catid/voron/kinematic_bed_brush_riser/BrushRiser16mmBolts.stl

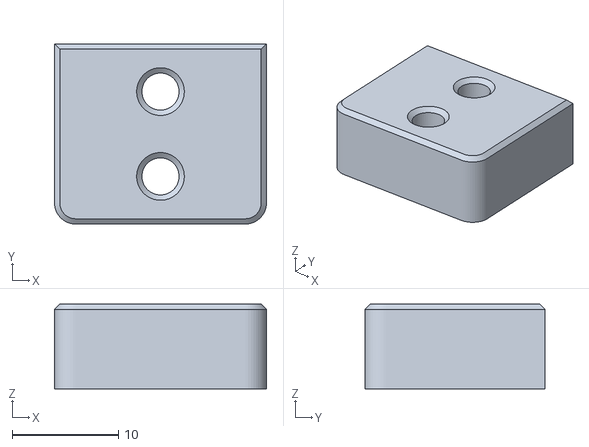
[picture p26: CAD file, 2022-04-16]
kinematic_bed_brush_riser/BrushRiser16mmBolts.stl
20.0 x 17.0 x 8.00
