catid/voron/printers/greenvoron/shaper_calibrate_x.png

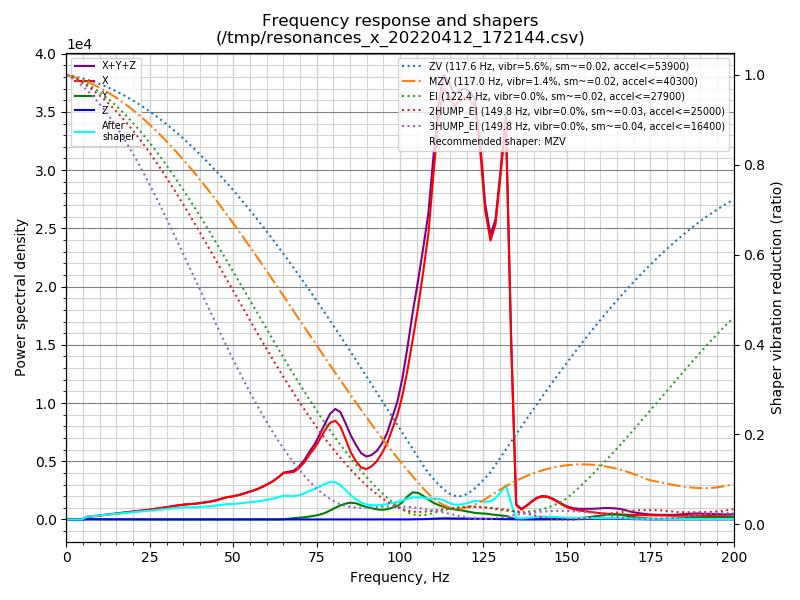
printers/greenvoron/shaper_calibrate_x.png
