catid/voron/printers/greenvoron/shaper_calibrate_y.png

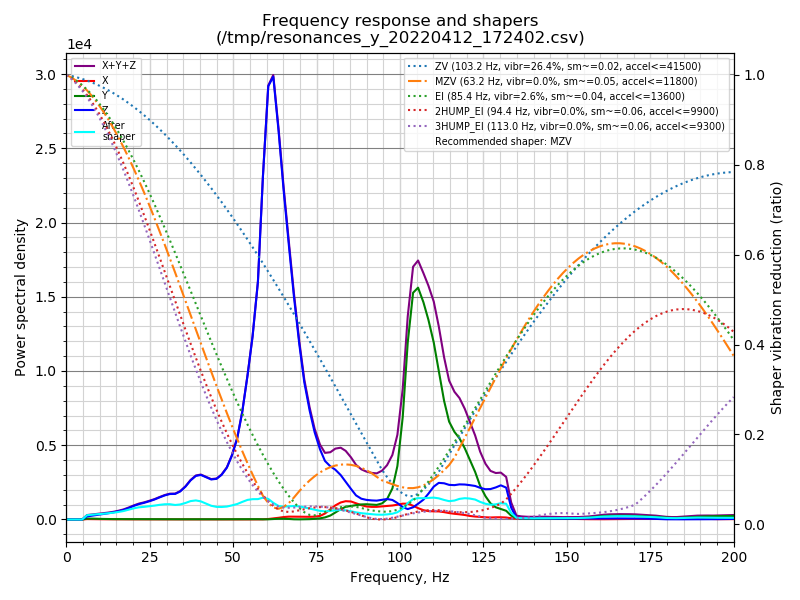
printers/greenvoron/shaper_calibrate_y.png
